LaskaKit/ESPink/img/espink-2-9inch.jpg

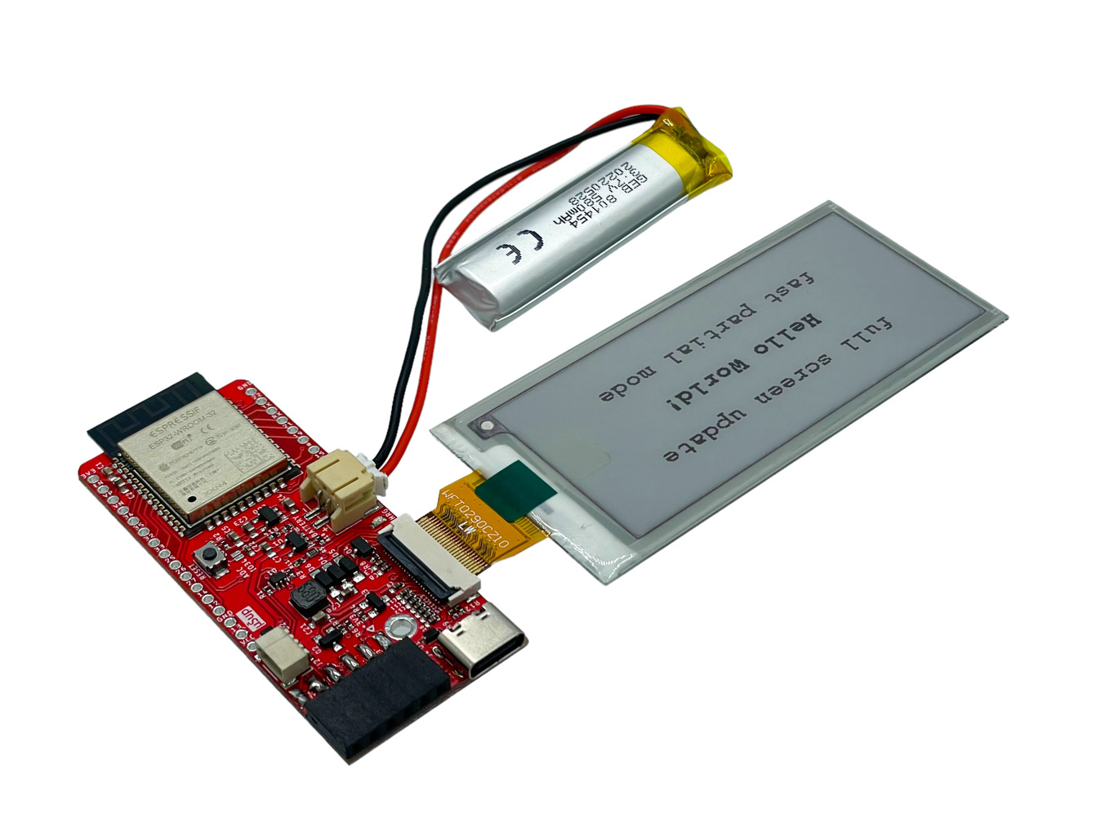
img/espink-2-9inch.jpg
