LaskaKit/ESPink/img/espink-7-5inch.jpg

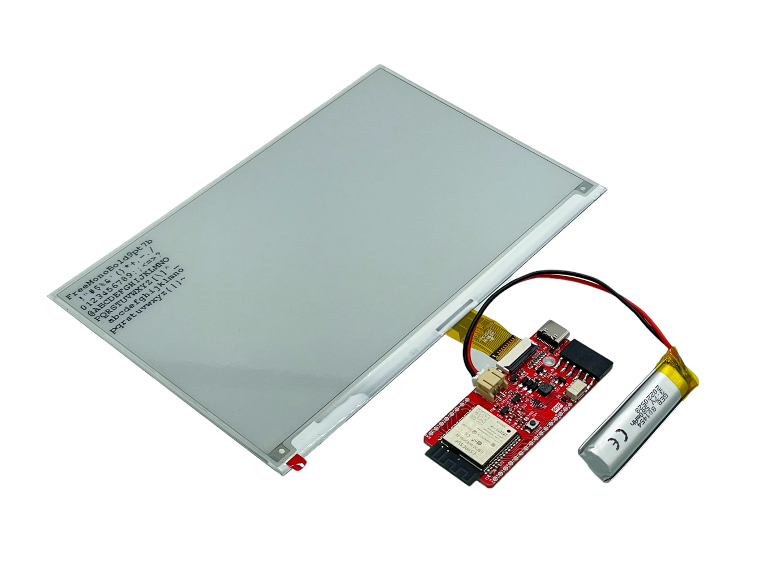
img/espink-7-5inch.jpg
