LaskaKit/ESPink/img/ESPink_v2-5_front.png

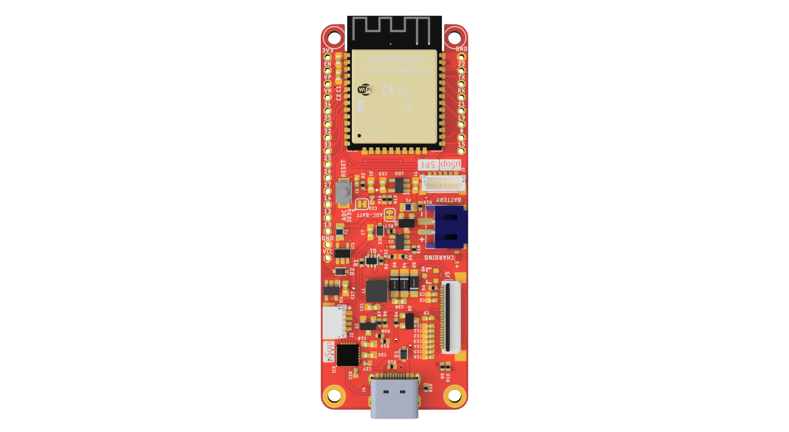
img/ESPink_v2-5_front.png
