LaskaKit/ESPink/img/LaskaKit-espink-2-7.jpg

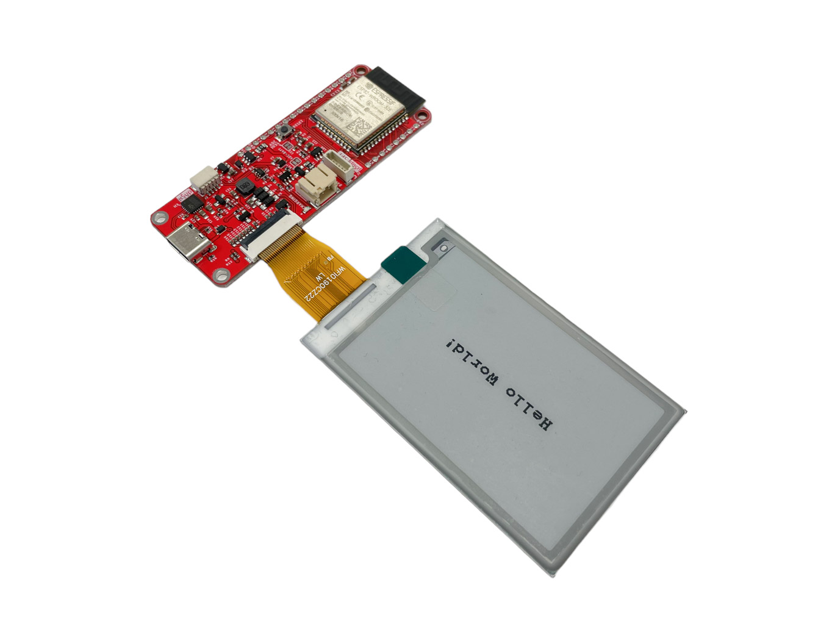
img/LaskaKit-espink-2-7.jpg
