LaskaKit/ESPink/img/LaskaKit-espink-2.jpg

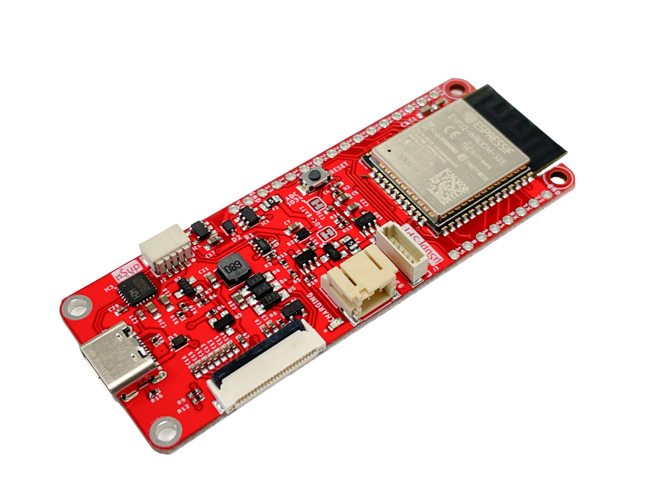
img/LaskaKit-espink-2.jpg
