LaskaKit/ESPink/img/LaskaKit-espink-3.jpg

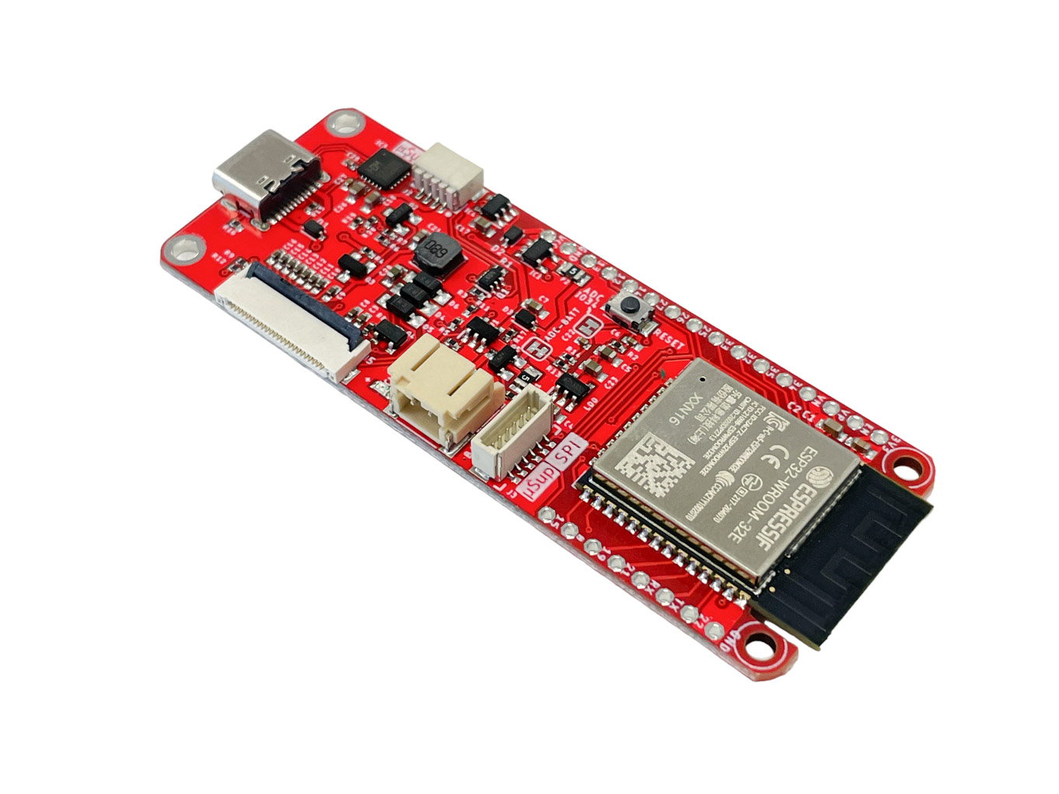
img/LaskaKit-espink-3.jpg
