LaskaKit/ESPink/img/LaskaKit-espink-4.jpg

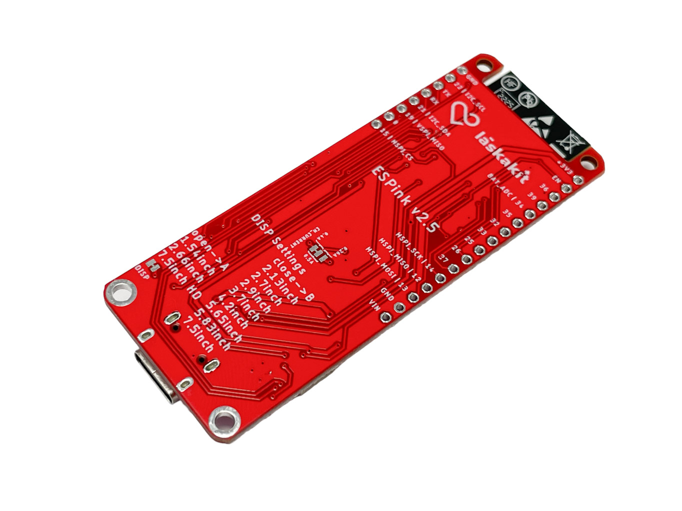
img/LaskaKit-espink-4.jpg
