LaskaKit/ESPink/img/LaskaKit-espink-esp32-e-paper-pcb-antenna-2.jpg

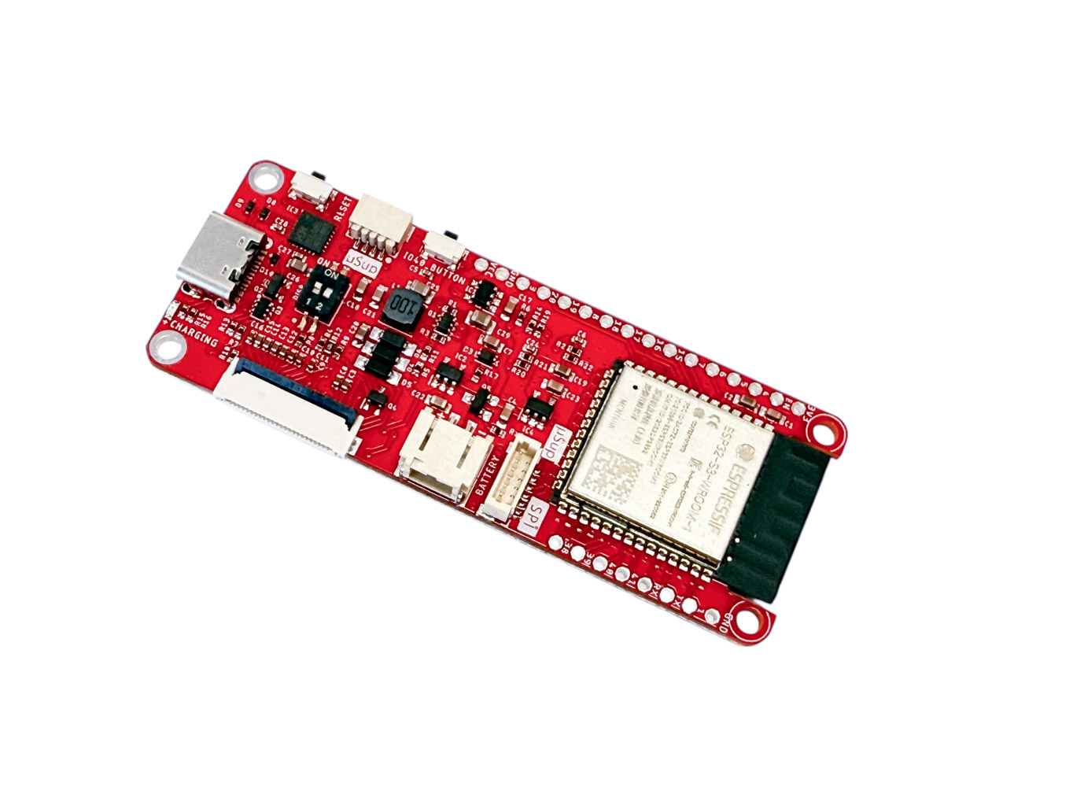
img/LaskaKit-espink-esp32-e-paper-pcb-antenna-2.jpg
