LaskaKit/ESPink/Production/espink_panel.jpg

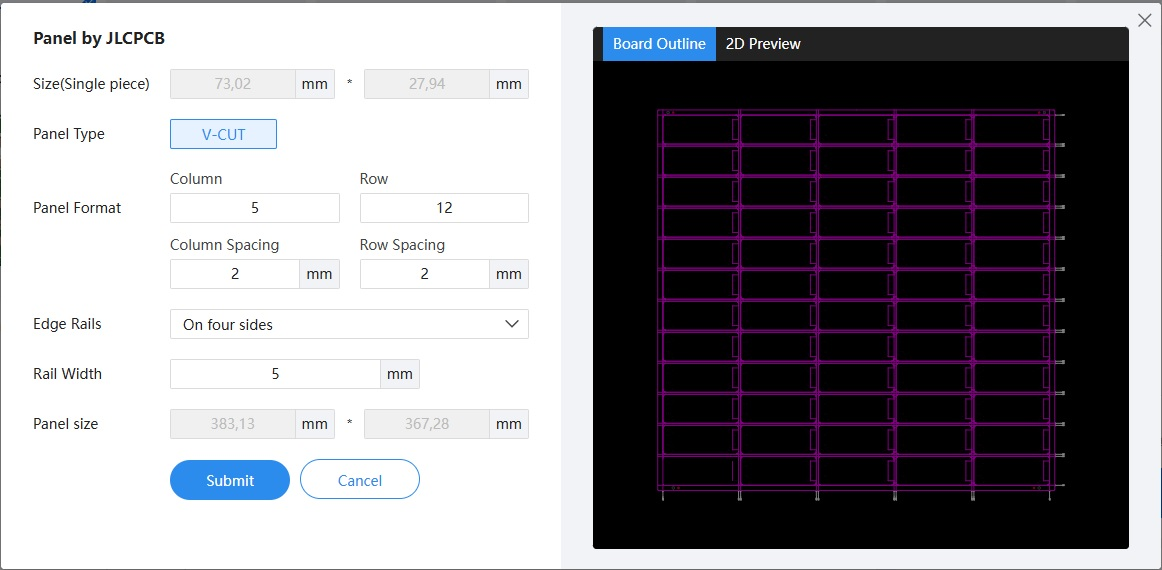
Production/espink_panel.jpg
