LaskaKit/ESPink/SW/ESPhome/byHavlas/back.jpg

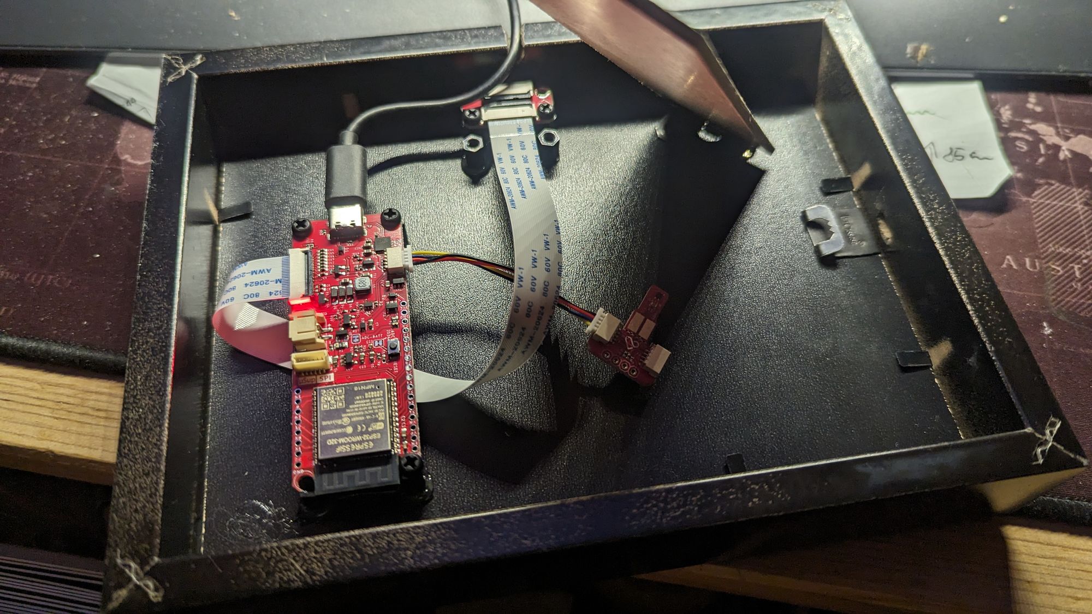
SW/ESPhome/byHavlas/back.jpg
