LaskaKit/ESPink/SW/ESPhome/byHavlas/face.jpg

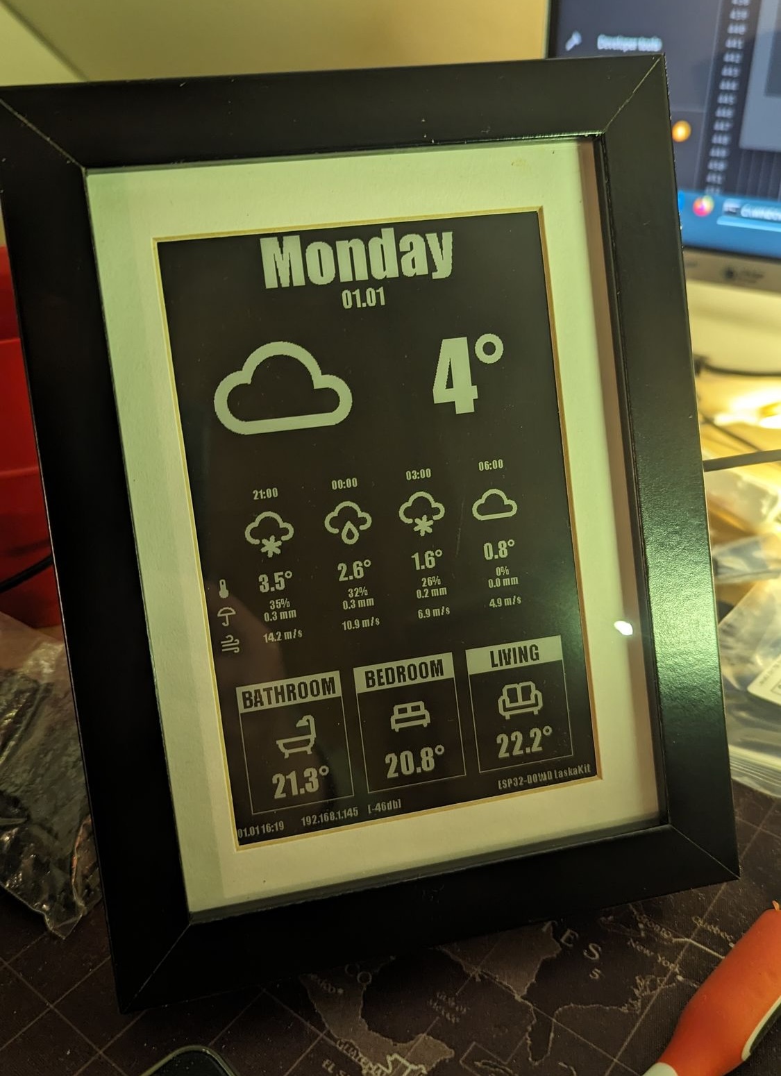
SW/ESPhome/byHavlas/face.jpg
