LaskaKit/ESPink/SW/GxEPD2_Just_Sleep/GxEPD2_display_selection.h

// Display Library example for SPI e-paper panels from Dalian Good Display and boards from Waveshare.
// Requires HW SPI and Adafruit_GFX. Caution: the e-paper panels require 3.3V supply AND data lines!
//
// Display Library based on Demo Example from Good Display: http://www.e-paper-display.com/download_list/downloadcategoryid=34&isMode=false.html
//
// Author: Jean-Marc Zingg
//
// Version: see library.properties
//
// Library: https://github.com/ZinggJM/GxEPD2

// Supporting Arduino Forum Topics:
// Waveshare e-paper displays with SPI: http://forum.arduino.cc/index.php?topic=487007.0
// Good Display ePaper for Arduino: https://forum.arduino.cc/index.php?topic=436411.0

#if defined(ESP32)
// select one and adapt to your mapping, can use full buffer size (full HEIGHT)
//GxEPD2_BW<GxEPD2_102, GxEPD2_102::HEIGHT> display(GxEPD2_102(/*CS=5*/ SS, /*DC=*/ 17, /*RST=*/ 16, /*BUSY=*/ 4)); // GDEW0102T4
//GxEPD2_BW<GxEPD2_154, GxEPD2_154::HEIGHT> display(GxEPD2_154(/*CS=5*/ SS, /*DC=*/ 17, /*RST=*/ 16, /*BUSY=*/ 4)); // GDEP015OC1 no longer available
//GxEPD2_BW<GxEPD2_154_D67, GxEPD2_154_D67::HEIGHT> display(GxEPD2_154_D67(/*CS=5*/ SS, /*DC=*/ 17, /*RST=*/ 16, /*BUSY=*/ 4)); // GDEH0154D67, LaskaKit: Waveshare 1.54"
//GxEPD2_BW<GxEPD2_154_T8, GxEPD2_154_T8::HEIGHT> display(GxEPD2_154_T8(/*CS=5*/ SS, /*DC=*/ 17, /*RST=*/ 16, /*BUSY=*/ 4)); // GDEW0154T8 152x152
//GxEPD2_BW<GxEPD2_154_M09, GxEPD2_154_M09::HEIGHT> display(GxEPD2_154_M09(/*CS=5*/ SS, /*DC=*/ 17, /*RST=*/ 16, /*BUSY=*/ 4)); // GDEW0154M09 200x200
//GxEPD2_BW<GxEPD2_154_M10, GxEPD2_154_M10::HEIGHT> display(GxEPD2_154_M10(/*CS=5*/ SS, /*DC=*/ 17, /*RST=*/ 16, /*BUSY=*/ 4)); // GDEW0154M10 152x152
//GxEPD2_BW<GxEPD2_213, GxEPD2_213::HEIGHT> display(GxEPD2_213(/*CS=5*/ SS, /*DC=*/ 17, /*RST=*/ 16, /*BUSY=*/ 4)); // GDE0213B1, phased out
//GxEPD2_BW<GxEPD2_213_B72, GxEPD2_213_B72::HEIGHT> display(GxEPD2_213_B72(/*CS=5*/ SS, /*DC=*/ 17, /*RST=*/ 16, /*BUSY=*/ 4)); // GDEH0213B72
//GxEPD2_BW<GxEPD2_213_B73, GxEPD2_213_B73::HEIGHT> display(GxEPD2_213_B73(/*CS=5*/ SS, /*DC=*/ 17, /*RST=*/ 16, /*BUSY=*/ 4)); // GDEH0213B73
//GxEPD2_BW<GxEPD2_213_B74, GxEPD2_213_B74::HEIGHT> display(GxEPD2_213_B74(/*CS=5*/ SS, /*DC=*/ 17, /*RST=*/ 16, /*BUSY=*/ 4)); // GDEM0213B74
//GxEPD2_BW<GxEPD2_213_flex, GxEPD2_213_flex::HEIGHT> display(GxEPD2_213_flex(/*CS=5*/ SS, /*DC=*/ 17, /*RST=*/ 16, /*BUSY=*/ 4)); // GDEW0213I5F
//GxEPD2_BW<GxEPD2_213_M21, GxEPD2_213_M21::HEIGHT> display(GxEPD2_213_M21(/*CS=5*/ SS, /*DC=*/ 17, /*RST=*/ 16, /*BUSY=*/ 4)); // GDEW0213M21
//GxEPD2_BW<GxEPD2_213_T5D, GxEPD2_213_T5D::HEIGHT> display(GxEPD2_213_T5D(/*CS=5*/ SS, /*DC=*/ 17, /*RST=*/ 16, /*BUSY=*/ 4)); // GDEW0213T5D
//GxEPD2_BW<GxEPD2_290, GxEPD2_290::HEIGHT> display(GxEPD2_290(/*CS=5*/ SS, /*DC=*/ 17, /*RST=*/ 16, /*BUSY=*/ 4)); // GDEH029A1
//GxEPD2_BW<GxEPD2_290_T5, GxEPD2_290_T5::HEIGHT> display(GxEPD2_290_T5(/*CS=5*/ SS, /*DC=*/ 17, /*RST=*/ 16, /*BUSY=*/ 4)); // GDEW029T5
//GxEPD2_BW<GxEPD2_290_T5D, GxEPD2_290_T5D::HEIGHT> display(GxEPD2_290_T5D(/*CS=5*/ SS, /*DC=*/ 17, /*RST=*/ 16, /*BUSY=*/ 4)); // GDEW029T5D
//GxEPD2_BW<GxEPD2_290_I6FD, GxEPD2_290_I6FD::HEIGHT> display(GxEPD2_290_I6FD(/*CS=5*/ SS, /*DC=*/ 17, /*RST=*/ 16, /*BUSY=*/ 4)); // GDEW029I6FD
//GxEPD2_BW<GxEPD2_290_T94, GxEPD2_290_T94::HEIGHT> display(GxEPD2_290_T94(/*CS=5*/ SS, /*DC=*/ 17, /*RST=*/ 16, /*BUSY=*/ 4)); // GDEM029T94
//GxEPD2_BW<GxEPD2_290_T94_V2, GxEPD2_290_T94_V2::HEIGHT> display(GxEPD2_290_T94_V2(/*CS=5*/ SS, /*DC=*/ 17, /*RST=*/ 16, /*BUSY=*/ 4)); // GDEM029T94, Waveshare 2.9" V2 variant
//GxEPD2_BW<GxEPD2_290_M06, GxEPD2_290_M06::HEIGHT> display(GxEPD2_290_M06(/*CS=5*/ SS, /*DC=*/ 17, /*RST=*/ 16, /*BUSY=*/ 4)); // GDEW029M06
//GxEPD2_BW<GxEPD2_260, GxEPD2_260::HEIGHT> display(GxEPD2_260(/*CS=5*/ SS, /*DC=*/ 17, /*RST=*/ 16, /*BUSY=*/ 4)); // GDEW026T0
//GxEPD2_BW<GxEPD2_260_M01, GxEPD2_260_M01::HEIGHT> display(GxEPD2_260_M01(/*CS=5*/ SS, /*DC=*/ 17, /*RST=*/ 16, /*BUSY=*/ 4)); // GDEW026M01
//GxEPD2_BW<GxEPD2_270, GxEPD2_270::HEIGHT> display(GxEPD2_270(/*CS=5*/ SS, /*DC=*/ 17, /*RST=*/ 16, /*BUSY=*/ 4)); // GDEW027W3
//GxEPD2_BW<GxEPD2_371, GxEPD2_371::HEIGHT> display(GxEPD2_371(/*CS=5*/ SS, /*DC=*/ 17, /*RST=*/ 16, /*BUSY=*/ 4)); // GDEW0371W7
//GxEPD2_BW<GxEPD2_370_TC1, GxEPD2_370_TC1::HEIGHT> display(GxEPD2_370_TC1(/*CS=5*/ SS, /*DC=*/ 17, /*RST=*/ 16, /*BUSY=*/ 4)); // ED037TC1, Waveshare 3.7"
//GxEPD2_BW<GxEPD2_420, GxEPD2_420::HEIGHT> display(GxEPD2_420(/*CS=5*/ SS, /*DC=*/ 17, /*RST=*/ 16, /*BUSY=*/ 4)); // GDEW042T2
//GxEPD2_BW<GxEPD2_420_M01, GxEPD2_420_M01::HEIGHT> display(GxEPD2_420_M01(/*CS=5*/ SS, /*DC=*/ 17, /*RST=*/ 16, /*BUSY=*/ 4)); // GDEW042M01, LaskaKit: Waveshare 4.2"
//GxEPD2_BW<GxEPD2_583, GxEPD2_583::HEIGHT> display(GxEPD2_583(/*CS=5*/ SS, /*DC=*/ 17, /*RST=*/ 16, /*BUSY=*/ 4)); // GDEW0583T7
//GxEPD2_BW<GxEPD2_583_T8, GxEPD2_583_T8::HEIGHT> display(GxEPD2_583_T8(/*CS=5*/ SS, /*DC=*/ 17, /*RST=*/ 16, /*BUSY=*/ 4)); // GDEW0583T8  648x480
//GxEPD2_BW<GxEPD2_750, GxEPD2_750::HEIGHT> display(GxEPD2_750(/*CS=5*/ SS, /*DC=*/ 17, /*RST=*/ 16, /*BUSY=*/ 4)); // GDEW075T8   640x384


GxEPD2_BW<GxEPD2_750_T7, GxEPD2_750_T7::HEIGHT> display(GxEPD2_750_T7(/*CS=5*/ SS, /*DC=*/ 17, /*RST=*/ 16, /*BUSY=*/ 4)); // GDEW075T7 800x480,  LaskaKit: Waveshare 7.5"
//GxEPD2_BW < GxEPD2_1160_T91, GxEPD2_1160_T91::HEIGHT / 2> display(GxEPD2_1160_T91(/*CS=5*/ SS, /*DC=*/ 17, /*RST=*/ 16, /*BUSY=*/ 4)); // GDEH116T91 960x640
// 3-color e-papers
//GxEPD2_3C<GxEPD2_154c, GxEPD2_154c::HEIGHT> display(GxEPD2_154c(/*CS=5*/ SS, /*DC=*/ 17, /*RST=*/ 16, /*BUSY=*/ 4)); // GDEW0154Z04 no longer available
//GxEPD2_3C<GxEPD2_154_Z90c, GxEPD2_154_Z90c::HEIGHT> display(GxEPD2_154_Z90c(/*CS=5*/ SS, /*DC=*/ 17, /*RST=*/ 16, /*BUSY=*/ 4)); // GDEH0154Z90, LaskaKit: Colour Waveshare 1.54"
//GxEPD2_3C<GxEPD2_213c, GxEPD2_213c::HEIGHT> display(GxEPD2_213c(/*CS=5*/ SS, /*DC=*/ 17, /*RST=*/ 16, /*BUSY=*/ 4)); // GDEW0213Z16
//GxEPD2_3C<GxEPD2_213_Z19c, GxEPD2_213_Z19c::HEIGHT> display(GxEPD2_213_Z19c(/*CS=5*/ SS, /*DC=*/ 17, /*RST=*/ 16, /*BUSY=*/ 4)); // GDEW0213Z19
//GxEPD2_3C<GxEPD2_213_Z98c, GxEPD2_213_Z98c::HEIGHT> display(GxEPD2_213_Z98c(/*CS=5*/ SS, /*DC=*/ 17, /*RST=*/ 16, /*BUSY=*/ 4)); // GDEY0213Z98
//GxEPD2_3C<GxEPD2_290c, GxEPD2_290c::HEIGHT> display(GxEPD2_290c(/*CS=5*/ SS, /*DC=*/ 17, /*RST=*/ 16, /*BUSY=*/ 4)); // GDEW029Z10
//GxEPD2_3C<GxEPD2_290_Z13c, GxEPD2_290_Z13c::HEIGHT> display(GxEPD2_290_Z13c(/*CS=5*/ SS, /*DC=*/ 17, /*RST=*/ 16, /*BUSY=*/ 4)); // GDEH029Z13
//GxEPD2_3C<GxEPD2_290_C90c, GxEPD2_290_C90c::HEIGHT> display(GxEPD2_290_C90c(/*CS=5*/ SS, /*DC=*/ 17, /*RST=*/ 16, /*BUSY=*/ 4)); // GDEM029C90
//GxEPD2_3C<GxEPD2_270c, GxEPD2_270c::HEIGHT> display(GxEPD2_270c(/*CS=5*/ SS, /*DC=*/ 17, /*RST=*/ 16, /*BUSY=*/ 4)); // GDEW027C44
//GxEPD2_3C<GxEPD2_420c, GxEPD2_420c::HEIGHT> display(GxEPD2_420c(/*CS=5*/ SS, /*DC=*/ 17, /*RST=*/ 16, /*BUSY=*/ 4)); // GDEW042Z15
//GxEPD2_3C<GxEPD2_420c_Z21, GxEPD2_420c_Z21::HEIGHT> display(GxEPD2_420c_Z21(/*CS=5*/ SS, /*DC=*/ 17, /*RST=*/ 16, /*BUSY=*/ 4)); // GDEQ042Z21
//GxEPD2_3C<GxEPD2_583c, GxEPD2_583c::HEIGHT> display(GxEPD2_583c(/*CS=5*/ SS, /*DC=*/ 17, /*RST=*/ 16, /*BUSY=*/ 4)); // GDEW0583Z21
//GxEPD2_3C<GxEPD2_750c, GxEPD2_750c::HEIGHT> display(GxEPD2_750c(/*CS=5*/ SS, /*DC=*/ 17, /*RST=*/ 16, /*BUSY=*/ 4)); // GDEW075Z09
//GxEPD2_3C<GxEPD2_750c_Z08, GxEPD2_750c_Z08::HEIGHT> display(GxEPD2_750c_Z08(/*CS=5*/ SS, /*DC=*/ 17, /*RST=*/ 16, /*BUSY=*/ 4)); // GDEW075Z08 800x480
//GxEPD2_3C<GxEPD2_750c_Z90, GxEPD2_750c_Z90::HEIGHT / 2> display(GxEPD2_750c_Z90(/*CS=5*/ SS, /*DC=*/ 17, /*RST=*/ 16, /*BUSY=*/ 4)); // GDEH075Z90 880x528
// 7-color e-paper
//GxEPD2_3C < GxEPD2_565c, GxEPD2_565c::HEIGHT / 2 > display(GxEPD2_565c(/*CS=5*/ SS, /*DC=*/ 17, /*RST=*/ 16, /*BUSY=*/ 4)); // Waveshare 5.65" 7-color (3C graphics)
//GxEPD2_7C < GxEPD2_565c, GxEPD2_565c::HEIGHT / 2 > display(GxEPD2_565c(/*CS=5*/ SS, /*DC=*/ 17, /*RST=*/ 16, /*BUSY=*/ 4)); // Waveshare 5.65" 7-color

// grey levels parallel IF e-papers on Waveshare e-Paper IT8951 Driver HAT
// HRDY -> 4, RST -> 16, CS -> SS(5), SCK -> SCK(18), MOSI -> MOSI(23), MISO -> MISO(19), GND -> GND, 5V -> 5V
// note: 5V supply needs to be exact and strong; 5V over diode from USB (e.g. Wemos D1 mini) doesn't work!
//GxEPD2_BW<GxEPD2_it60, GxEPD2_it60::HEIGHT> display(GxEPD2_it60(/*CS=5*/ SS, /*DC=*/ 17, /*RST=*/ 16, /*BUSY=*/ 4));
//GxEPD2_BW < GxEPD2_it60_1448x1072, GxEPD2_it60_1448x1072::HEIGHT / 4 > display(GxEPD2_it60_1448x1072(/*CS=5*/ SS, /*DC=*/ 17, /*RST=*/ 16, /*BUSY=*/ 4));
//GxEPD2_BW < GxEPD2_it78_1872x1404, GxEPD2_it78_1872x1404::HEIGHT / 8 > display(GxEPD2_it78_1872x1404(/*CS=5*/ SS, /*DC=*/ 17, /*RST=*/ 16, /*BUSY=*/ 4));

// Waveshare 12.48 b/w SPI display board and frame or Good Display 12.48 b/w panel GDEW1248T3
// general constructor for use with all parameters, e.g. for Waveshare ESP32 driver board mounted on connection board
//GxEPD2_BW < GxEPD2_1248, GxEPD2_1248::HEIGHT / 4 >
//display(GxEPD2_1248(/*sck=*/ 13, /*miso=*/ 12, /*mosi=*/ 14, /*cs_m1=*/ 23, /*cs_s1=*/ 22, /*cs_m2=*/ 16, /*cs_s2=*/ 19,
//                             /*dc1=*/ 25, /*dc2=*/ 17, /*rst1=*/ 33, /*rst2=*/ 5, /*busy_m1=*/ 32, /*busy_s1=*/ 26, /*busy_m2=*/ 18, /*busy_s2=*/ 4));
#endif
