LaskaKit/ESPink/SW/GDEY0154Z90_SHT40_ADC/OpenSansSB_12px.h

// Created by http://oleddisplay.squix.ch/ Consider a donation
// In case of problems make sure that you are using the font file with the correct version!
const uint8_t Open_Sans_SemiBold_12Bitmaps[] PROGMEM = {

	// Bitmap Data:
	0x00, // ' '
	0xAA,0xA2,0x80, // '!'
	0xAA,0xA0, // '"'
	0x12,0x0A,0x05,0x0F,0xE2,0x47,0xF0,0xA0,0x50,0x48,0x00, // '#'
	0x21,0xEA,0x38,0x70,0xE2,0xBC,0x20, // '$'
	0x63,0x0A,0x43,0x58,0x6A,0xC5,0xE8,0xD5,0x86,0xB0,0x94,0x31,0x80, // '%'
	0x70,0x64,0x32,0x0A,0x06,0x34,0x92,0x39,0x18,0x7A,0x00, // '&'
	0xA8, // '''
	0x4C,0x88,0x88,0x88,0x8C,0x40, // '('
	0x43,0x08,0x42,0x10,0x84,0x23,0x10, // ')'
	0x10,0x10,0x7C,0x10,0x28,0x28, // '*'
	0x20,0x8F,0x88,0x20, // '+'
	0x4B,0x00, // ','
	0xF0, // '-'
	0xA0, // '.'
	0x18,0x41,0x0C,0x21,0x84,0x10,0xC0, // '/'
	0x72,0x28,0xA2,0x8A,0x28,0xA2,0x70, // '0'
	0x33,0xAC,0x63,0x18,0xC6,0x30, // '1'
	0xF2,0x20,0x82,0x10,0xC6,0x30,0xF8, // '2'
	0xF2,0x20,0x86,0x70,0x20,0x82,0xF0, // '3'
	0x0C,0x1C,0x1C,0x2C,0x4C,0x4C,0xFE,0x0C,0x0C, // '4'
	0xFA,0x08,0x3C,0x18,0x20,0x86,0xF0, // '5'
	0x39,0x82,0x07,0xC8,0x91,0xA2,0x64,0x70, // '6'
	0xFE,0x04,0x0C,0x08,0x18,0x18,0x10,0x30,0x20, // '7'
	0x72,0x28,0xB6,0x73,0x68,0xA2,0xF8, // '8'
	0x72,0x68,0xA2,0x8B,0xE0,0x86,0xF0, // '9'
	0xA0,0xA0, // ':'
	0x48,0x00,0x96, // ';'
	0x08,0xEC,0x30,0x38,0x20, // '<'
	0xF8,0x0F,0x80, // '='
	0x83,0x81,0x86,0xE2,0x00, // '>'
	0xF0,0x61,0x84,0x20,0x80,0x18,0x60, // '?'
	0x3E,0x18,0x4D,0xEA,0xCA,0xA2,0xA8,0xAA,0x6A,0x6C,0x40,0x0F,0x80, // '@'
	0x18,0x0C,0x0F,0x04,0x82,0x43,0xF1,0x08,0x84,0xC3,0x00, // 'A'
	0xF9,0x9B,0x16,0x6F,0x98,0xB1,0x62,0xF8, // 'B'
	0x3E,0x40,0xC0,0x80,0x80,0x80,0xC0,0x40,0x3C, // 'C'
	0xF8,0xC4,0xC6,0xC2,0xC2,0xC2,0xC6,0xC4,0xF8, // 'D'
	0xFB,0x0C,0x30,0xFB,0x0C,0x30,0xF8, // 'E'
	0xFA,0x08,0x20,0xF2,0x08,0x20,0x80, // 'F'
	0x3E,0x60,0xC0,0x80,0x8E,0x82,0xC2,0x42,0x3E, // 'G'
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
};
const GFXglyph Open_Sans_SemiBold_12Glyphs[] PROGMEM = {
// bitmapOffset, width, height, xAdvance, xOffset, yOffset
	  {     0,   1,   1,   4,    0,    0 }, // ' '
	  {     1,   2,   9,   4,    1,   -9 }, // '!'
	  {     4,   4,   3,   6,    1,   -9 }, // '"'
	  {     6,   9,   9,   9,    0,   -9 }, // '#'
	  {    17,   6,   9,   8,    1,   -9 }, // '$'
	  {    24,  11,   9,  11,    0,   -9 }, // '%'
	  {    37,   9,   9,  10,    1,   -9 }, // '&'
	  {    48,   2,   3,   4,    1,   -9 }, // '''
	  {    49,   4,  11,   5,    1,   -9 }, // '('
	  {    55,   5,  11,   5,    0,   -9 }, // ')'
	  {    62,   8,   6,   8,    0,   -9 }, // '*'
	  {    68,   6,   5,   8,    1,   -7 }, // '+'
	  {    72,   3,   3,   4,    0,   -1 }, // ','
	  {    74,   5,   1,   5,    0,   -4 }, // '-'
	  {    75,   2,   2,   4,    1,   -2 }, // '.'
	  {    76,   6,   9,   6,    0,   -9 }, // '/'
	  {    83,   6,   9,   8,    1,   -9 }, // '0'
	  {    90,   5,   9,   8,    1,   -9 }, // '1'
	  {    96,   6,   9,   8,    1,   -9 }, // '2'
	  {   103,   6,   9,   8,    1,   -9 }, // '3'
	  {   110,   8,   9,   8,    0,   -9 }, // '4'
	  {   119,   6,   9,   8,    1,   -9 }, // '5'
	  {   126,   7,   9,   8,    1,   -9 }, // '6'
	  {   134,   8,   9,   8,    0,   -9 }, // '7'
	  {   143,   6,   9,   8,    1,   -9 }, // '8'
	  {   150,   6,   9,   8,    1,   -9 }, // '9'
	  {   157,   2,   6,   4,    1,   -6 }, // ':'
	  {   159,   3,   8,   4,    0,   -6 }, // ';'
	  {   162,   6,   6,   8,    1,   -8 }, // '<'
	  {   167,   6,   3,   8,    1,   -6 }, // '='
	  {   170,   6,   6,   8,    1,   -8 }, // '>'
	  {   175,   6,   9,   6,    0,   -9 }, // '?'
	  {   182,  10,  10,  12,    1,   -9 }, // '@'
	  {   195,   9,   9,   9,    0,   -9 }, // 'A'
	  {   206,   7,   9,   9,    1,   -9 }, // 'B'
	  {   214,   8,   9,   9,    1,   -9 }, // 'C'
	  {   223,   8,   9,  10,    1,   -9 }, // 'D'
	  {   232,   6,   9,   8,    1,   -9 }, // 'E'
	  {   239,   6,   9,   7,    1,   -9 }, // 'F'
	  {   246,   8,   9,  10,    1,   -9 }, // 'G'
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
};
const GFXfont OpenSansSB_12px PROGMEM = {
(uint8_t  *)Open_Sans_SemiBold_12Bitmaps,(GFXglyph *)Open_Sans_SemiBold_12Glyphs,0x20, 0x7E, 17};
